ferigan/vectrex-ll/Simulations/Vectrex-LL-Circuit-Y-Analogue-X-Digital.png

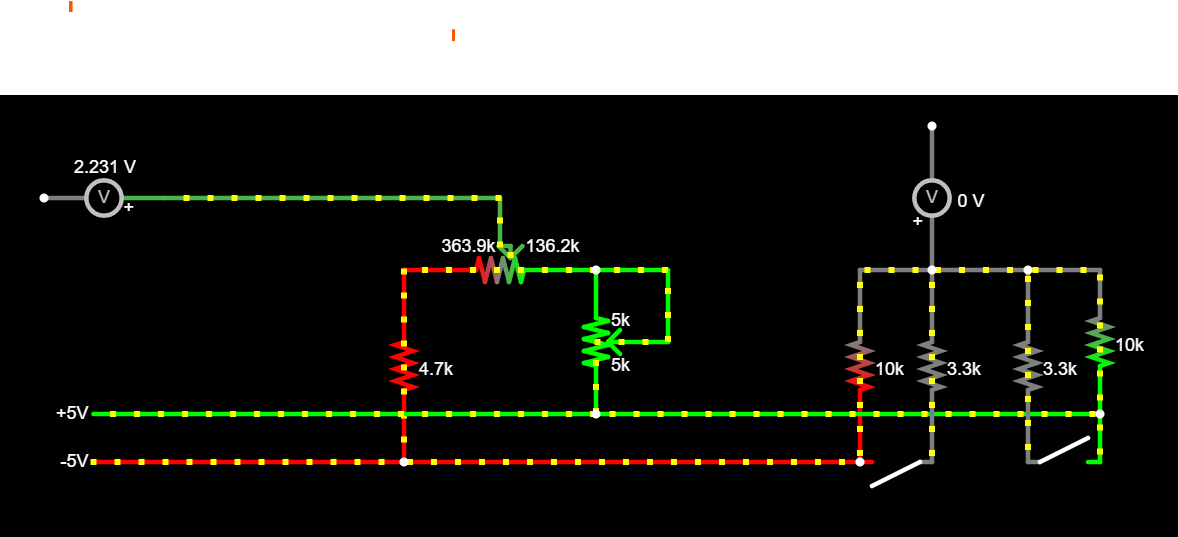
Simulations/Vectrex-LL-Circuit-Y-Analogue-X-Digital.png
