ferigan/vectrex-ll/Electronics/vectrex-ll-circuit-v4b BOM.png

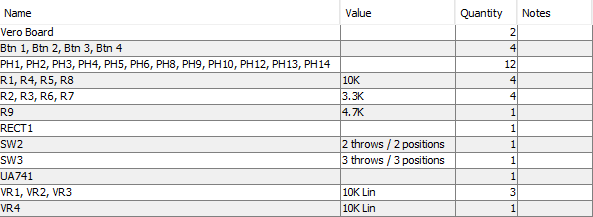
Electronics/vectrex-ll-circuit-v4b BOM.png
